cjhirashi/ct-prub-in/cuarto-pruebas/Documentación/Diagramas/CP INNES-AUT-E-CN-2.pdf

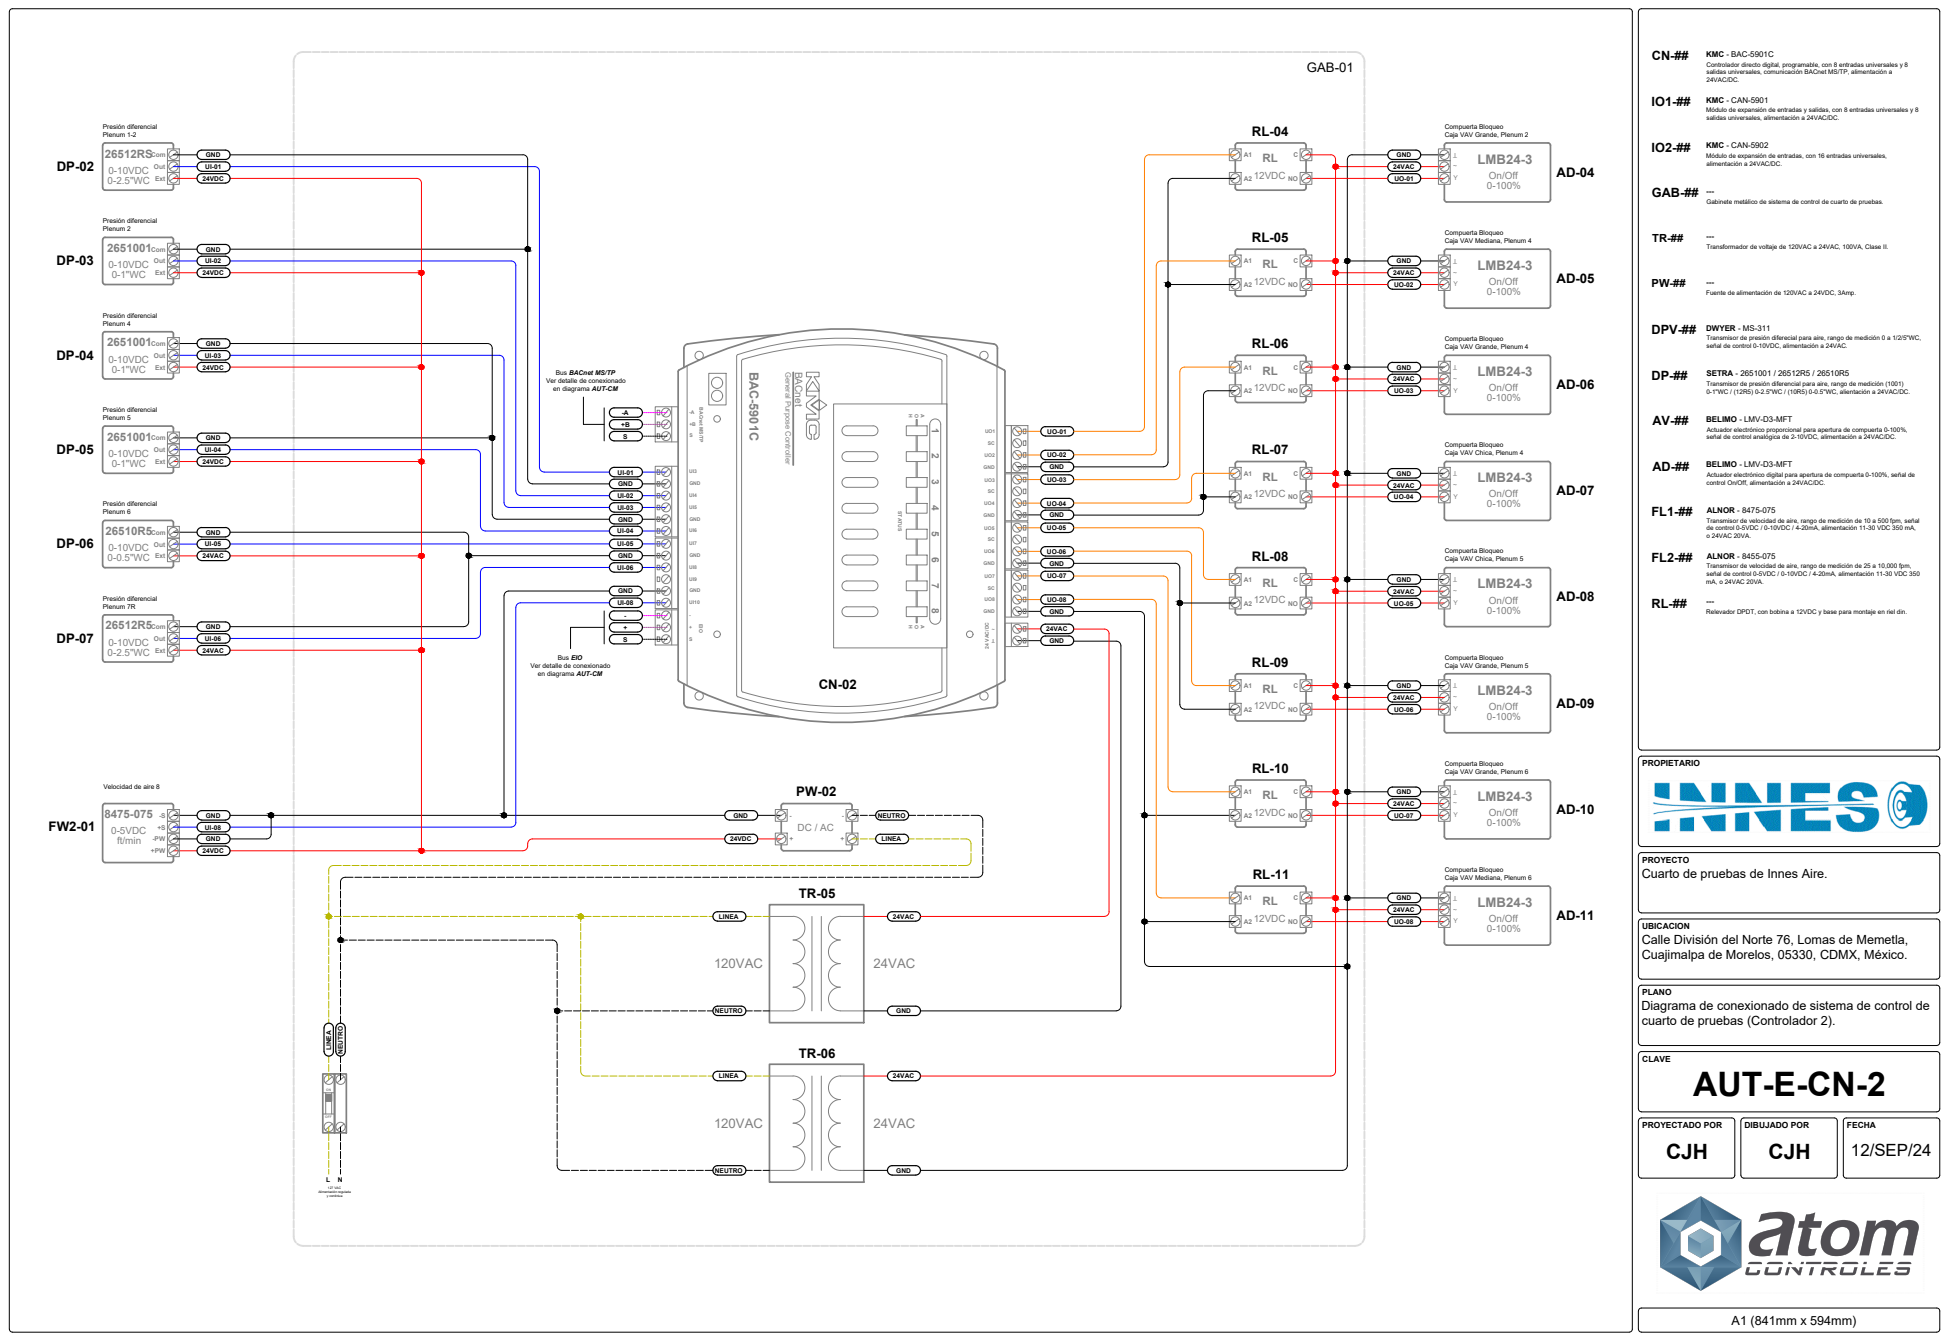
[picture p2: page 1]
Presión diferencial Plenum 1-2; Presión diferencial Plenum 2; 0-2.5"WC Ext; 0-1"WC Ext; 127 VAC Alimentación regulada y continiua; 12VDC NOC; UI3 GND; UI4 UI5 GND; UI7 GND; UI8 UI9 GND; BAC-5901C; General Purpose Controller; BACnet; HOA HOA STATUS; Bus EIO; Presión diferencial Plenum 4; Presión diferencial Plenum 5; Presión diferencial Plenum 6; 0-0.5"WC Ext; Presión diferencial Plenum 7R; PROYECTADO POR; DIBUJADO POR; FECHA

KMC - BAC-5901C
Controlador directo digital, programable, con 8 entradas universales y 8
salidas universales, comunicación BACnet MS/TP, alimentación a
24VAC/DC.

KMC - CAN-5901
Módulo de expansión de entradas y salidas, con 8 entradas universales y 8
salidas universales, alimentación a 24VAC/DC.

Compuerta Bloqueo
Caja VAV Grande, Plenum 2
LMB24-3
On/Off

KMC - CAN-5902
Módulo de expansión de entradas, con 16 entradas universales,
alimentación a 24VAC/DC.

Gabinete metálico de sistema de control de cuarto de pruebas. ---

Caja VAV Mediana, Plenum 4

Transformador de voltaje de 120VAC a 24VAC, 100VA, Clase II. ---

Fuente de alimentación de 120VAC a 24VDC, 3Amp. ---

DWYER - MS-311
Transmisor de presión diferecial para aire, rango de medición 0 a 1/2/5"WC,
señal de control 0-10VDC, alimentación a 24VAC.

Caja VAV Grande, Plenum 4

Bus BACnet MS/TP
Ver detalle de conexionado
en diagrama AUT-CM

SETRA - 2651001 / 26512R5 / 26510R5
Transmisor de presión diferencial para aire, rango de medición (1001)
0-1"WC / (12R5) 0-2.5"WC / (10R5) 0-0.5"WC, alientación a 24VAC/DC.

UI6 BACnet MS/TP -+S EIO

BELIMO - LMV-D3-MFT
Actuador electrónico proporcional para apertura de compuerta 0-100%,
señal de control analógica de 2-10VDC, alimentación a 24VAC/DC.

Caja VAV Chica, Plenum 4

Actuador electrónico digital para apertura de compuerta 0-100%, señal de
control On/Off, alimentación a 24VAC/DC.

ALNOR - 8475-075
Transmisor de velocidad de aire, rango de medición de 10 a 500 fpm, señal
de control 0-5VDC / 0-10VDC / 4-20mA, alimentación 11-30 VDC 350 mA,
o 24VAC 20VA.

Caja VAV Chica, Plenum 5

ALNOR - 8455-075
Transmisor de velocidad de aire, rango de medición de 25 a 10,000 fpm,
señal de control 0-5VDC / 0-10VDC / 4-20mA, alimentación 11-30 VDC 350
mA, o 24VAC 20VA.

GND~T 24 VAC/DC

Relevador DPDT, con bobina a 12VDC y base para montaje en riel din. ---

Caja VAV Grande, Plenum 5 T~Y

Caja VAV Grande, Plenum 6

Velocidad de aire 8

PROYECTO
Cuarto de pruebas de Innes Aire.

Caja VAV Mediana, Plenum 6

UBICACION
Calle División del Norte 76, Lomas de Memetla,
Cuajimalpa de Morelos, 05330, CDMX, México.

PLANO
Diagrama de conexionado de sistema de control de
cuarto de pruebas (Controlador 2).
AUT-E-CN-2

NEUTRO LINEA NEUTRO
