cjhirashi/ct-prub-in/cuarto-pruebas/Documentación/Diagramas/CP INNES-AUT-E-IO1-2.pdf

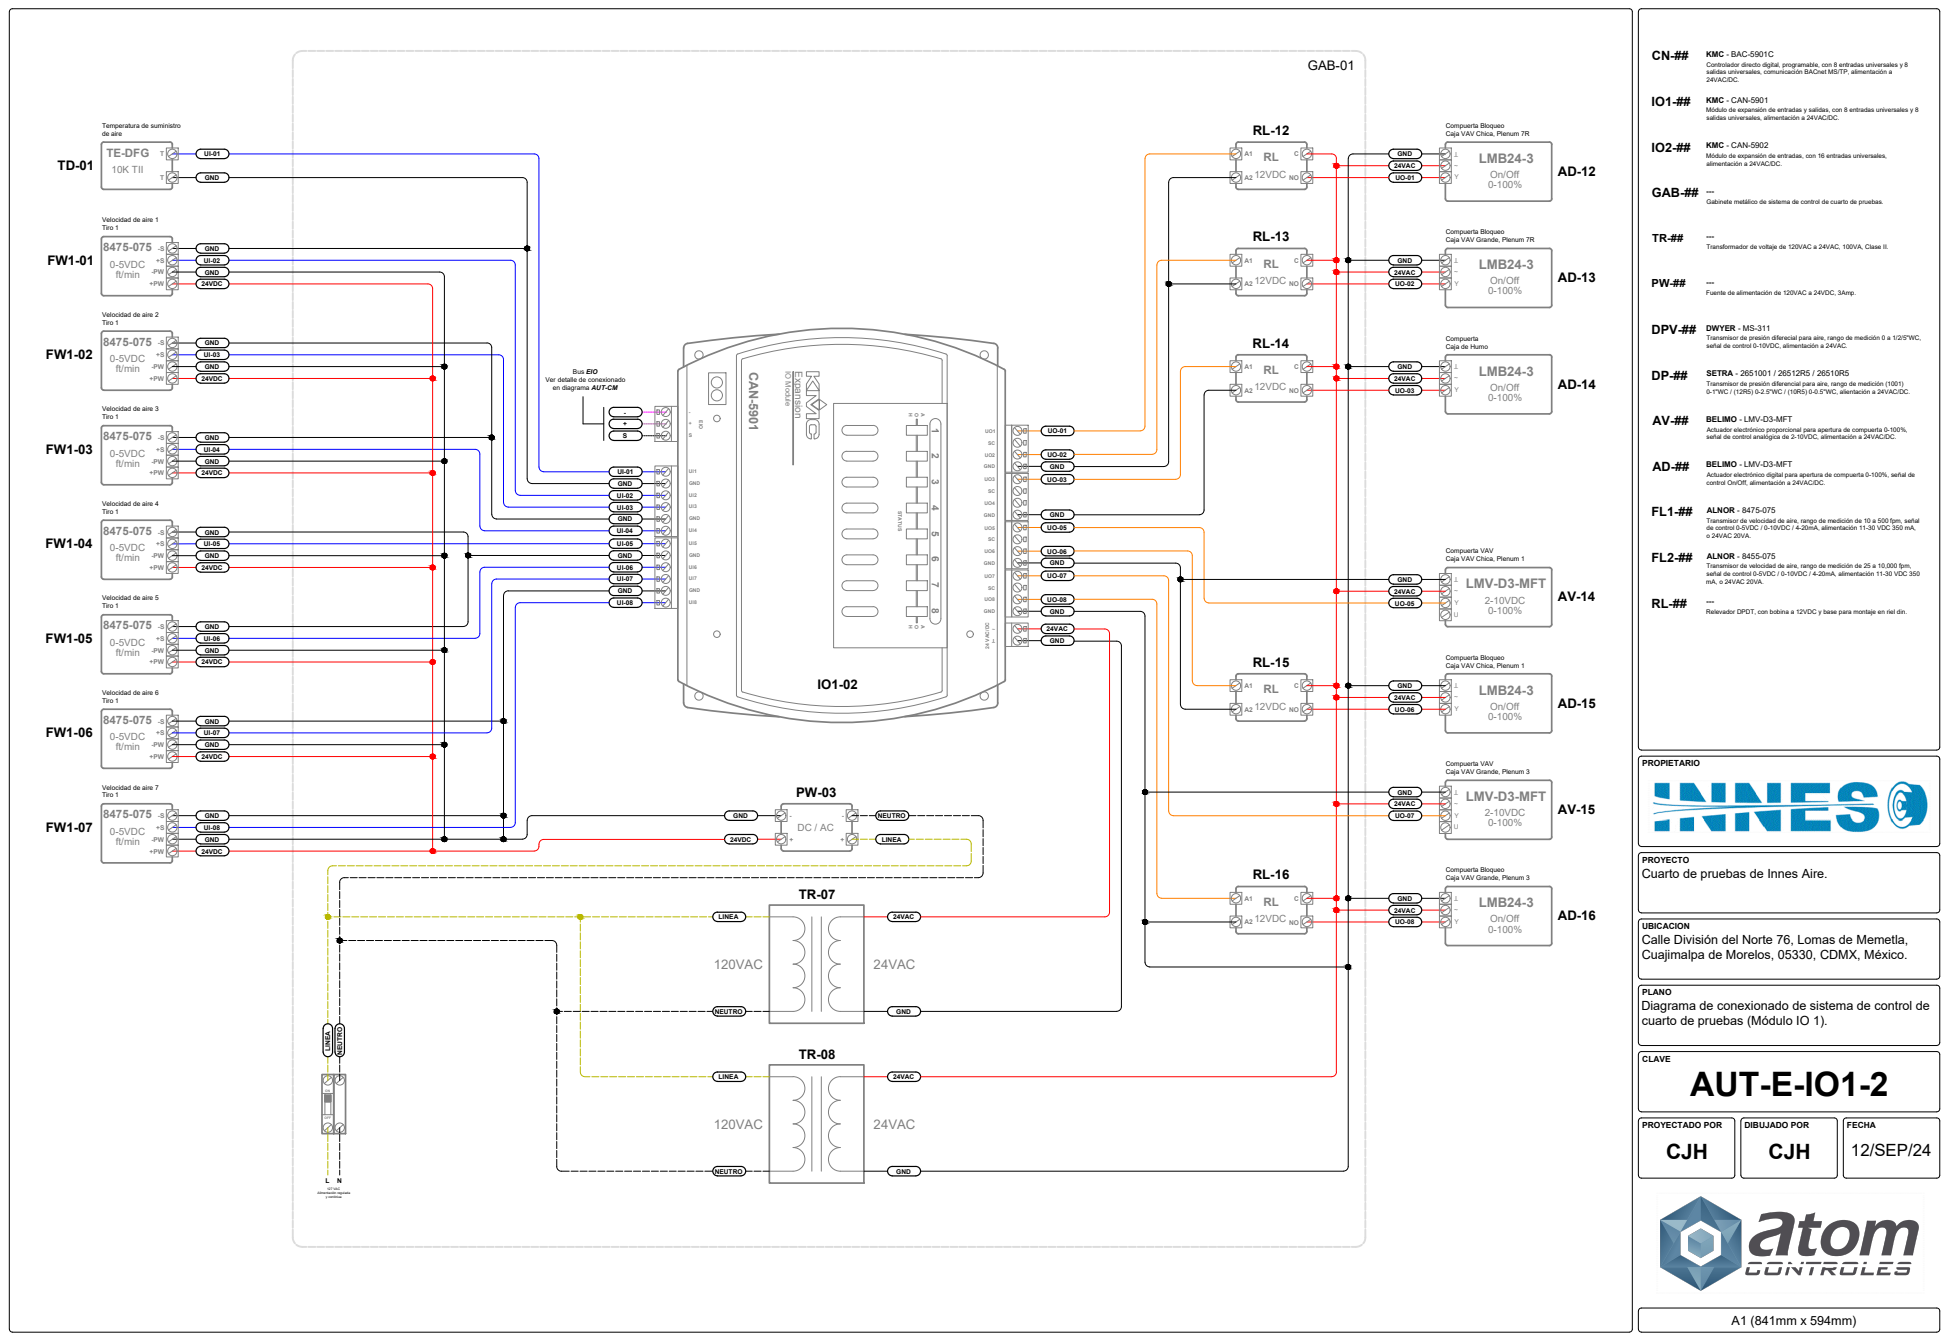
[picture p4: page 1]
127 VAC Alimentación regulada y continiua; 12VDC NOC; 10K TII; Velocidad de aire 1 Tiro 1; Bus EIO; UI1 GND; UI2 UI3 GND; UI4 -+S EIO; UI5 GND; UI6 UI7 GND; CAN-5901; IO Module; Expansion; HOA HOA STATUS; Velocidad de aire 2 Tiro 1; Velocidad de aire 3 Tiro 1; Velocidad de aire 4 Tiro 1; Velocidad de aire 5 Tiro 1; Velocidad de aire 6 Tiro 1; Velocidad de aire 7 Tiro 1; PROYECTADO POR; DIBUJADO POR; FECHA

KMC - BAC-5901C
Controlador directo digital, programable, con 8 entradas universales y 8
salidas universales, comunicación BACnet MS/TP, alimentación a
24VAC/DC.

KMC - CAN-5901
Módulo de expansión de entradas y salidas, con 8 entradas universales y 8
salidas universales, alimentación a 24VAC/DC.

Temperatura de suministro
de aire
TE-DFG

Compuerta Bloqueo
Caja VAV Chica, Plenum 7R
LMB24-3

KMC - CAN-5902
Módulo de expansión de entradas, con 16 entradas universales,
alimentación a 24VAC/DC.

Gabinete metálico de sistema de control de cuarto de pruebas. ---

Caja VAV Grande, Plenum 7R

Transformador de voltaje de 120VAC a 24VAC, 100VA, Clase II. ---

Fuente de alimentación de 120VAC a 24VDC, 3Amp. ---

DWYER - MS-311
Transmisor de presión diferecial para aire, rango de medición 0 a 1/2/5"WC,
señal de control 0-10VDC, alimentación a 24VAC.

Compuerta
Caja de Humo
On/Off

SETRA - 2651001 / 26512R5 / 26510R5
Transmisor de presión diferencial para aire, rango de medición (1001)
0-1"WC / (12R5) 0-2.5"WC / (10R5) 0-0.5"WC, alientación a 24VAC/DC.

Ver detalle de conexionado
en diagrama AUT-CM

BELIMO - LMV-D3-MFT
Actuador electrónico proporcional para apertura de compuerta 0-100%,
señal de control analógica de 2-10VDC, alimentación a 24VAC/DC.

Actuador electrónico digital para apertura de compuerta 0-100%, señal de
control On/Off, alimentación a 24VAC/DC.

ALNOR - 8475-075
Transmisor de velocidad de aire, rango de medición de 10 a 500 fpm, señal
de control 0-5VDC / 0-10VDC / 4-20mA, alimentación 11-30 VDC 350 mA,
o 24VAC 20VA.

Compuerta VAV
Caja VAV Chica, Plenum 1 T~YU
LMV-D3-MFT
2-10VDC

ALNOR - 8455-075
Transmisor de velocidad de aire, rango de medición de 25 a 10,000 fpm,
señal de control 0-5VDC / 0-10VDC / 4-20mA, alimentación 11-30 VDC 350
mA, o 24VAC 20VA.

GND~T 24 VAC/DC

Relevador DPDT, con bobina a 12VDC y base para montaje en riel din. ---

Caja VAV Chica, Plenum 1 T~Y

Caja VAV Grande, Plenum 3 T~YU

PROYECTO
Cuarto de pruebas de Innes Aire.

Caja VAV Grande, Plenum 3

UBICACION
Calle División del Norte 76, Lomas de Memetla,
Cuajimalpa de Morelos, 05330, CDMX, México.

PLANO
Diagrama de conexionado de sistema de control de
cuarto de pruebas (Módulo IO 1).
AUT-E-IO1-2

NEUTRO LINEA NEUTRO
