cjhirashi/ct-prub-in/cuarto-pruebas/Documentación/Diagramas/CP INNES-AUT-E-IO2-1.pdf

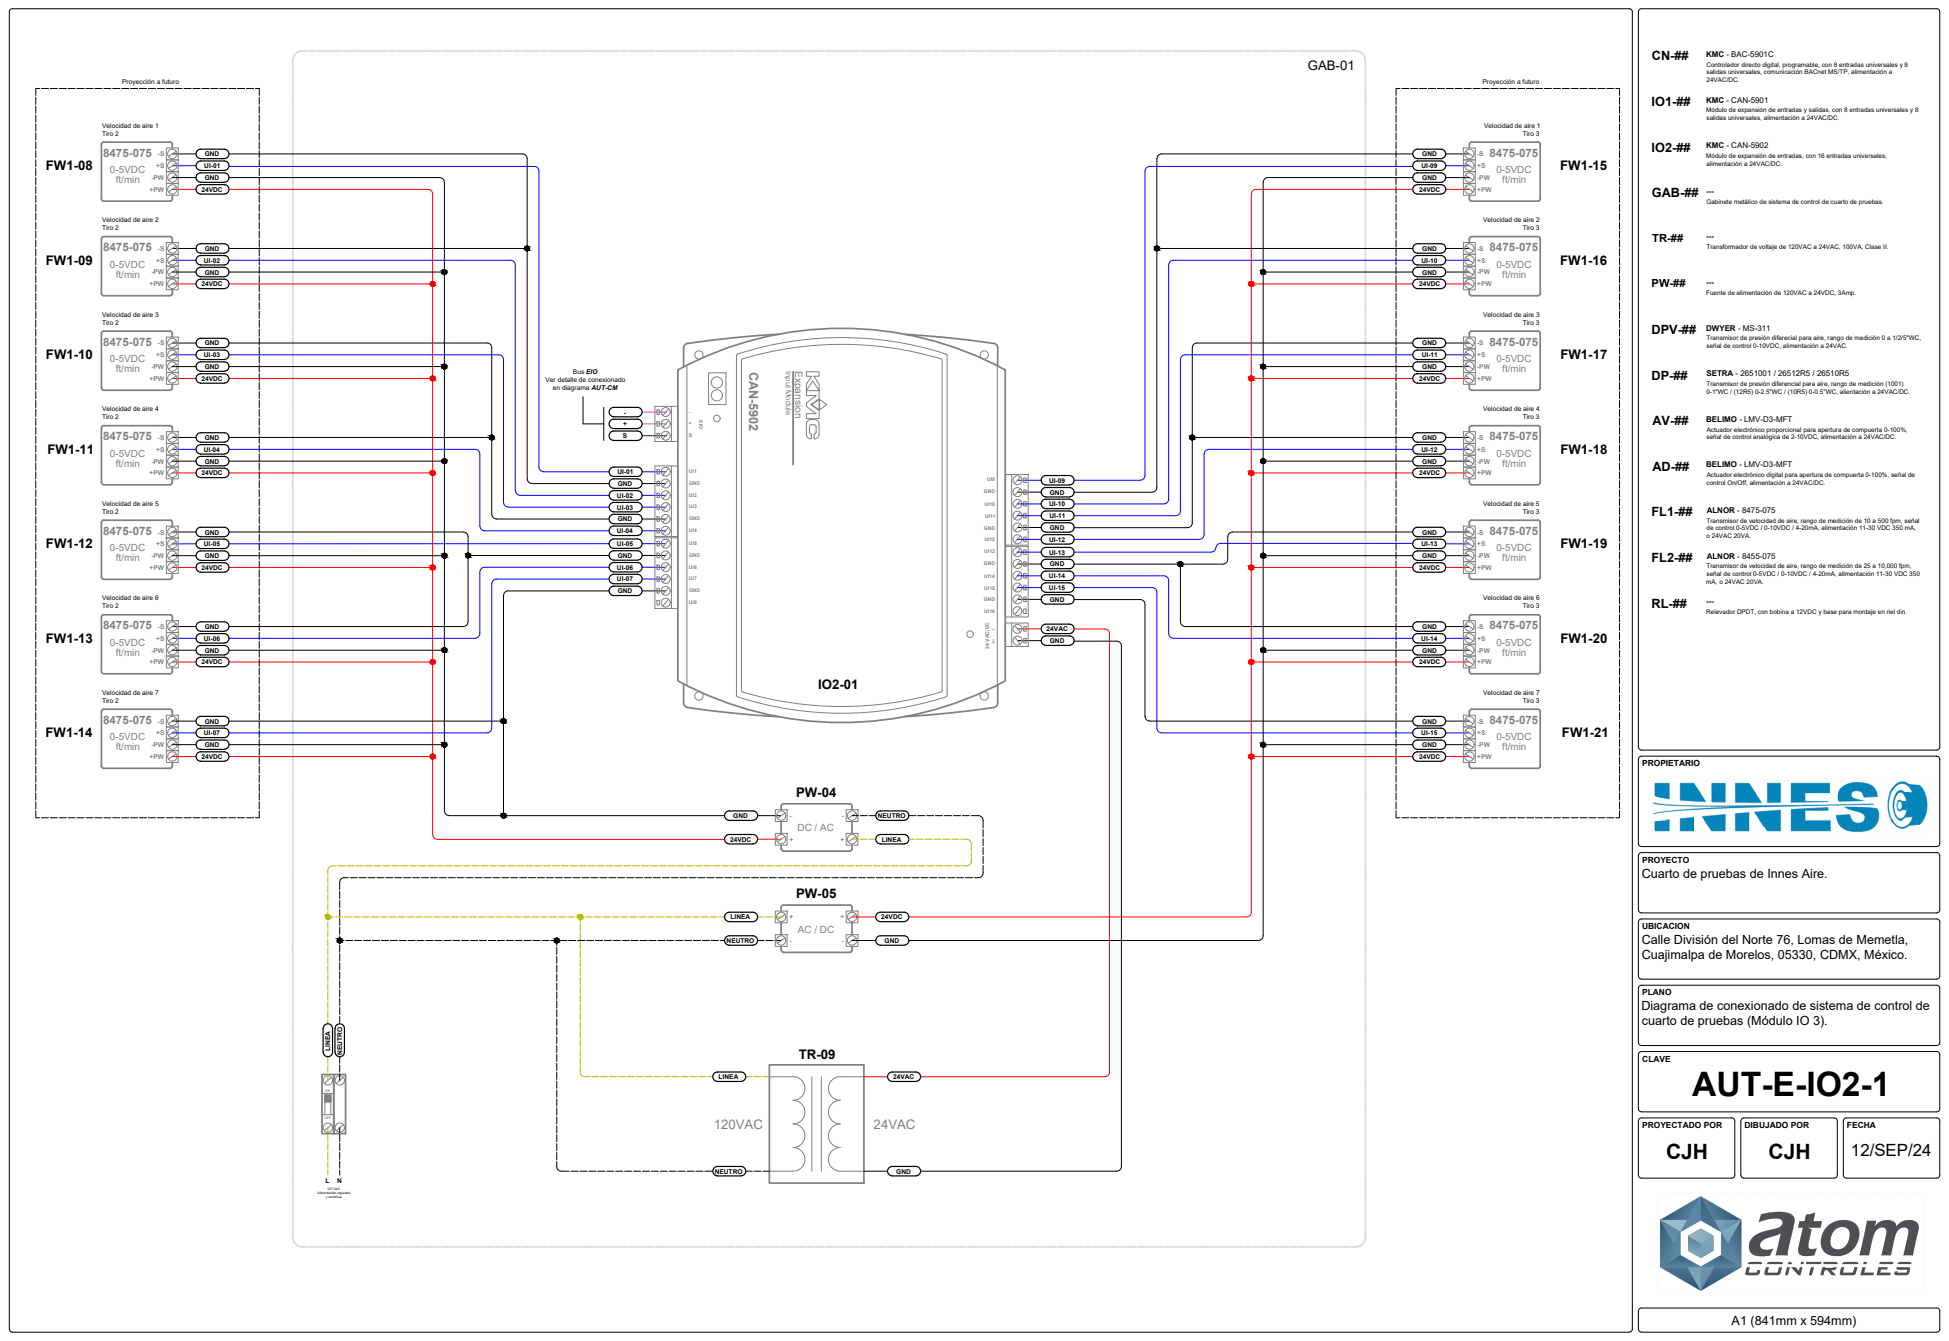
[picture p5: page 1]
127 VAC Alimentación regulada y continiua; Velocidad de aire 2; Tiro 2; Bus EIO; Velocidad de aire 3 Tiro 2; Velocidad de aire 4 Tiro 2; Velocidad de aire 5 Tiro 2; Velocidad de aire 6 Tiro 2; Velocidad de aire 7 Tiro 2; UI13 GND; UI14 UI15 GND; UI16~T 24 VAC/DC; UI1 GND; UI2 UI3 GND; UI4 -+S EIO; UI5 GND; UI6 UI7 GND; CAN-5902; Input Module; UI9 GND; UI10 UI11 GND; GND; Velocidad de aire 1 Tiro 2; Tiro 3; Proyección a futuro; PROYECTADO POR; DIBUJADO POR; FECHA

KMC - BAC-5901C
Controlador directo digital, programable, con 8 entradas universales y 8
salidas universales, comunicación BACnet MS/TP, alimentación a
24VAC/DC.

KMC - CAN-5901
Módulo de expansión de entradas y salidas, con 8 entradas universales y 8
salidas universales, alimentación a 24VAC/DC.

Velocidad de aire 1

KMC - CAN-5902
Módulo de expansión de entradas, con 16 entradas universales,
alimentación a 24VAC/DC.

Gabinete metálico de sistema de control de cuarto de pruebas. ---

Velocidad de aire 2

Transformador de voltaje de 120VAC a 24VAC, 100VA, Clase II. ---

Fuente de alimentación de 120VAC a 24VDC, 3Amp. ---

Velocidad de aire 3

DWYER - MS-311
Transmisor de presión diferecial para aire, rango de medición 0 a 1/2/5"WC,
señal de control 0-10VDC, alimentación a 24VAC.

SETRA - 2651001 / 26512R5 / 26510R5
Transmisor de presión diferencial para aire, rango de medición (1001)
0-1"WC / (12R5) 0-2.5"WC / (10R5) 0-0.5"WC, alientación a 24VAC/DC.

Ver detalle de conexionado
en diagrama AUT-CM

Velocidad de aire 4

BELIMO - LMV-D3-MFT
Actuador electrónico proporcional para apertura de compuerta 0-100%,
señal de control analógica de 2-10VDC, alimentación a 24VAC/DC.

Actuador electrónico digital para apertura de compuerta 0-100%, señal de
control On/Off, alimentación a 24VAC/DC.

Velocidad de aire 5

ALNOR - 8475-075
Transmisor de velocidad de aire, rango de medición de 10 a 500 fpm, señal
de control 0-5VDC / 0-10VDC / 4-20mA, alimentación 11-30 VDC 350 mA,
o 24VAC 20VA.

ALNOR - 8455-075
Transmisor de velocidad de aire, rango de medición de 25 a 10,000 fpm,
señal de control 0-5VDC / 0-10VDC / 4-20mA, alimentación 11-30 VDC 350
mA, o 24VAC 20VA.

Velocidad de aire 6

Relevador DPDT, con bobina a 12VDC y base para montaje en riel din. ---

Velocidad de aire 7

PROYECTO
Cuarto de pruebas de Innes Aire.

UBICACION
Calle División del Norte 76, Lomas de Memetla,
Cuajimalpa de Morelos, 05330, CDMX, México.

PLANO
Diagrama de conexionado de sistema de control de
cuarto de pruebas (Módulo IO 3).
AUT-E-IO2-1

NEUTRO LINEA NEUTRO
