cjhirashi/ct-prub-in/Cuarto-de-Pruebas/Cajas-VAV.md

# Cajas VAV de Cuarto de Pruebas

Las **Cajas VAV** (Variable Air Volume) son componentes clave en el subsistema del Cuarto de Pruebas, diseñadas para regular el flujo de aire en los plenums. Cada VAV permite un control preciso para pruebas de rendimiento y ajustes en tiempo real.

## Componentes Principales de Cada Caja VAV

1. **Sensor de Caudal**:
   - Mide el flujo de aire para garantizar el ajuste preciso según las necesidades de prueba.
   - Comunicación: Integrado al controlador principal vía entradas universales.

2. **Actuador Proporcional**:
   - Controla la apertura y cierre de la compuerta principal de la VAV.
   - Tipo: Proporcional para ajustes continuos según la demanda.

3. **Actuador On/Off**:
   - Controla una compuerta de bloqueo en la caja VAV.
   - Tipo: Binario, asegurando que la caja esté completamente activa o cerrada según se requiera.

## Distribución de las Cajas VAV en los Plenums

### PLENUM 1
- **VAV 01 - Mediana**
  - Tamaño: 8 pulgadas
  - Área: 0.3382 pies²
  - CV: 817
- **VAV 02 - Grande**
  - Tamaño: 14 pulgadas
  - Área: 1.05 pies²
  - CV: 2474
- **VAV 03 - Chica**
  - Tamaño: 4 pulgadas
  - Área: 0.0819 pies²
  - CV: 209

### PLENUM 2
- **VAV 01 - Mediana**
  - Tamaño: 7 pulgadas
  - Área: 0.2578 pies²
  - CV: 612
- **VAV 02 - Grande**
  - Tamaño: 12 pulgadas
  - Área: 0.7691 pies²
  - CV: 1792

### PLENUM 3
- **VAV 01 - Grande**
  - Tamaño: 10 pulgadas
  - Área: 0.5319 pies²
  - CV: 1250

### PLENUM 4
- **VAV 01 - Mediana**
  - Tamaño: 8 pulgadas
  - Área: 0.3382 pies²
  - CV: 817
- **VAV 02 - Grande**
  - Tamaño: 14 pulgadas
  - Área: 1.05 pies²
  - CV: 2474
- **VAV 03 - Chica**
  - Tamaño: 4 pulgadas
  - Área: 0.0819 pies²
  - CV: 209

### PLENUM 5
- **VAV 01 - Chica**
  - Tamaño: 5 pulgadas
  - Área: 0.1296 pies²
  - CV: 315
- **VAV 02 - Grande**
  - Tamaño: 16 pulgadas
  - Área: 1.3745 pies²
  - CV: 3235

### PLENUM 6
- **VAV 01 - Grande**
  - Tamaño: 14 pulgadas
  - Área: 1.05 pies²
  - CV: 2474
- **VAV 02 - Mediana**
  - Tamaño: 8 pulgadas
  - Área: 0.3382 pies²
  - CV: 817

### PLENUM 7 (Retorno)
- **VAV 01 - Chica**
  - Tamaño: 4 pulgadas
  - Área: 0.0819 pies²
  - CV: 209
- **VAV 02 - Grande**
  - Tamaño: 14 pulgadas
  - Área: 1.05 pies²
  - CV: 2474

## Funcionalidades Clave de las Cajas VAV

1. **Regulación del Flujo de Aire**:
   - Ajustan dinámicamente el caudal para mantener las condiciones ideales en el Cuarto de Pruebas.
2. **Control de Presión**:
   - Los sensores de presión diferencial trabajan en conjunto con los actuadores para garantizar un flujo estable.
3. **Compatibilidad con BACnet MS/TP**:
   - Integradas a la red para supervisión y control centralizado.
