cjhirashi/ct-prub-in/Cuarto-de-Pruebas/VAVs.md

# Cajas VAV de cuarto de pruebas

## PLENUM 1

> CAUDAL `AV9`.10021 ***CFM***

#### VAV 01 - **MEDIANA** 

> ***CONTROLADOR 1***

> Tamaño `8` ***pulgadas***
>
> Area `0.3382` ***pies2***
>
> CV `817`
>
> DP `AI3`.10021 ***"WC***
>
> CAUDAL `AV1`.10021 ***CFM***
>
> MULTIPLICADOR `AV2`.10021
>
> OFFSET `AV3`.10021
>
> CAUDAL Cal `AV4`.10021 ***CFM***
>
> ====================
>
> COMPUERTA `AO1`.10021 ***%***
>
> COMP BLOQ `BO14`.10021 ***%***
>
> ====================
>
> DEMANDA `AV85`.10021 ***%***

#### VAV 02 - **GRANDE** 

> ***CONTROLADOR 1***

> Tamaño `14` ***pulgadas***
>
> Area `1.05` ***pies2***
>
> CV `2474`
>
> DP `AI4`.10021 ***"WC***
>
> CAUDAL `AV5`.10021 ***CFM***
>
> MULTIPLICADOR `AV6`.10021
>
> OFFSET `AV7`.10021
>
> CAUDAL Cal `AV8`.10021 ***CFM***
>
> ====================
>
> COMPUERTA `AO2`.10021 ***%***
>
> COMP BLOQ `BO15`.10021 ***%***
>
> ====================
>
> DEMANDA `AV86`.10021 ***%***

#### VAV 03 - **CHICA** 

> ***CONTROLADOR 2***

> Tamaño `4` ***pulgadas***
>
> Area `0.0819` ***pies2***
>
> CV `209`
>
> DP `AI7`.10022 ***"WC***
>
> CAUDAL `AV1`.10022 ***CFM***
>
> MULTIPLICADOR `AV2`.10022
>
> OFFSET `AV3`.10022
>
> CAUDAL Cal `AV4`.10022 ***CFM***
>
> ====================
>
> COMPUERTA `AO13`.10022 ***%***
>
> COMP BLOQ `BO14`.10022 ***%***
>
> ====================
>
> DEMANDA `AV14`.10022 ***%***

## PLENUM 2

> CAUDAL `AV18`.10021 ***CFM***

#### VAV 01 - **MEDIANA** 

> ***CONTROLADOR 1***

> Tamaño `7` ***pulgadas***
>
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
>
> CAUDAL `AV54`.10021 ***CFM***
>
> MULTIPLICADOR `AV55`.10021
>
> OFFSET `AV56`.10021
>
> CAUDAL Cal `AV57`.10021 ***CFM***
>
> ====================
>
> COMPUERTA `AO13`.10021 ***%***
>
> COMP BLOQ `BO10`.10022 ***%*** **REMOTO**
>
> ====================
>
> DEMANDA `AV97`.10021 ***%***
