cjhirashi/ct-prub-in/CUARTO-PRUEBAS/10021_CNTR-1/VAVS.md

# Cajas VAV de cuarto de pruebas

## PLENUM 1

- VAV 01

- VAV 02

- VAV 03

## PLENUM 2

- VAV 01

- VAV 02

## PLENUM 3

- VAV 01

## PLENUM 4

- VAV 01

- VAV 02

- VAV 03

## PLENUM 5

- VAV 01

- VAV 02

## PLENUM 6

- VAV 01

- VAV 02

## PLENUM 7 RETORNO

- VAV 01

- VAV 02
