cjhirashi/ct-prub-in/UMA-01/10003_UMA-01/PRG7_CUARTO_PRUEBAS.txt

REM PRG7_CUARTO_PRUEBAS (CONTROL: UMA 01)
REM CONTROL DE ACTIVACION DESDE CONTROL DE CUARTO DE PRUEBAS
REM AUTHOR CARLOS JIMENEZ HIRASHI @cjhirashi
REM VERSION 1.0.0

REM SINCRONIZACION CON CONTROLADOR CUARTO DE PRUEBAS

	REM *VARIABLE DE ACTIVACIÓN

		IF INTERVAL(00:00:02) THEN
			BV32 = 10021.BV1
			IF BV32 = 1 THEN 10021.BV2 = BV3 ELSE 10021.BV2 = 0
		ENDIF

	REM *BLOQUEO DE MODO DE ARRANQUE

		IF BV32 = 1 THEN
			MSV1@7 = 4
		 ELSE
			RLQ MSV1@7
		ENDIF

END
